fcipaq/picoheld_hardware/board/board_assembled_render.png

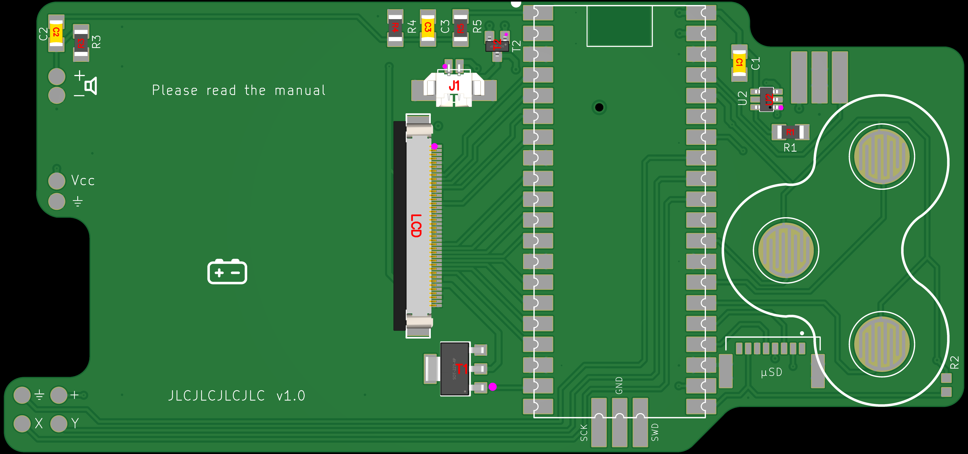
board/board_assembled_render.png
